AccidentalMachines/PocketQueen-v1/Firmware/PocketQueenFirmware_v1.0/bpm_bitmap.c

#define bpm_bitmap_width 17
#define bpm_bitmap_height 7
static unsigned char bpm_bitmap_bits[] = {
   0xc7, 0x11, 0x01, 0x49, 0xb2, 0x01, 0x49, 0x52, 0x01, 0xc7, 0x11, 0x01,
   0x49, 0x10, 0x01, 0x49, 0x10, 0x01, 0x47, 0x10, 0x01 };
