AccidentalMachines/PocketQueen-v1/Firmware/PocketQueenFirmware_v1.0/swg_bitmap.c

#define swg_bitmap_width 17
#define swg_bitmap_height 8
static unsigned char swg_bitmap_bits[] = {
   0x46, 0xc4, 0x00, 0x49, 0x24, 0x01, 0x41, 0x24, 0x00, 0x42, 0x24, 0x00,
   0x44, 0xa5, 0x01, 0x48, 0x25, 0x01, 0xc9, 0x26, 0x01, 0x46, 0xc4, 0x00 };
